BrianAtwell/Wood-DVD-Shelves/ShortShelf/ShortShelfRenderSide.png

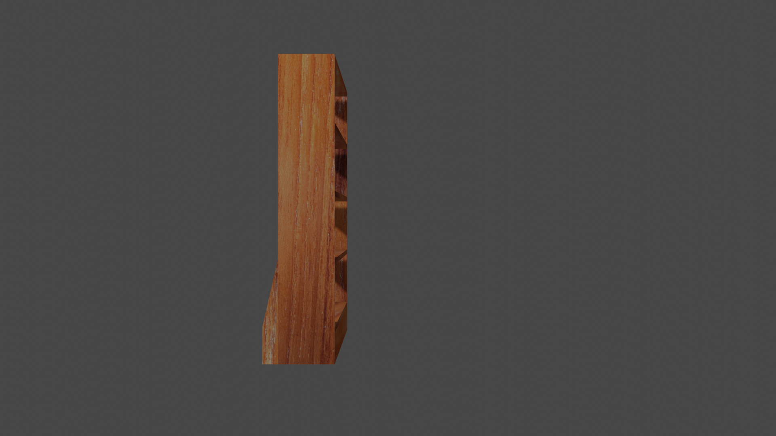
ShortShelf/ShortShelfRenderSide.png
